VasilKalchev/PXLstick/img/3d-diag-bg.png

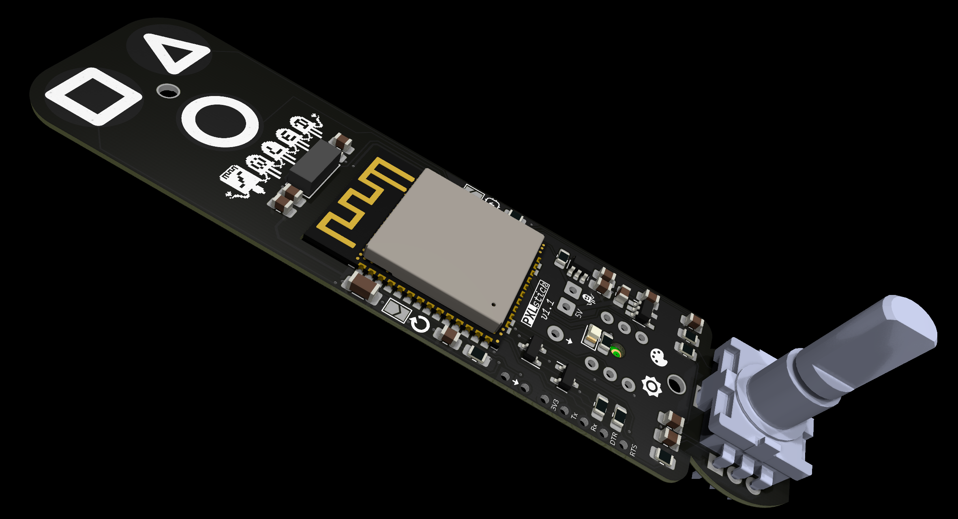
img/3d-diag-bg.png
