VasilKalchev/PXLstick/img/3d-diag.png

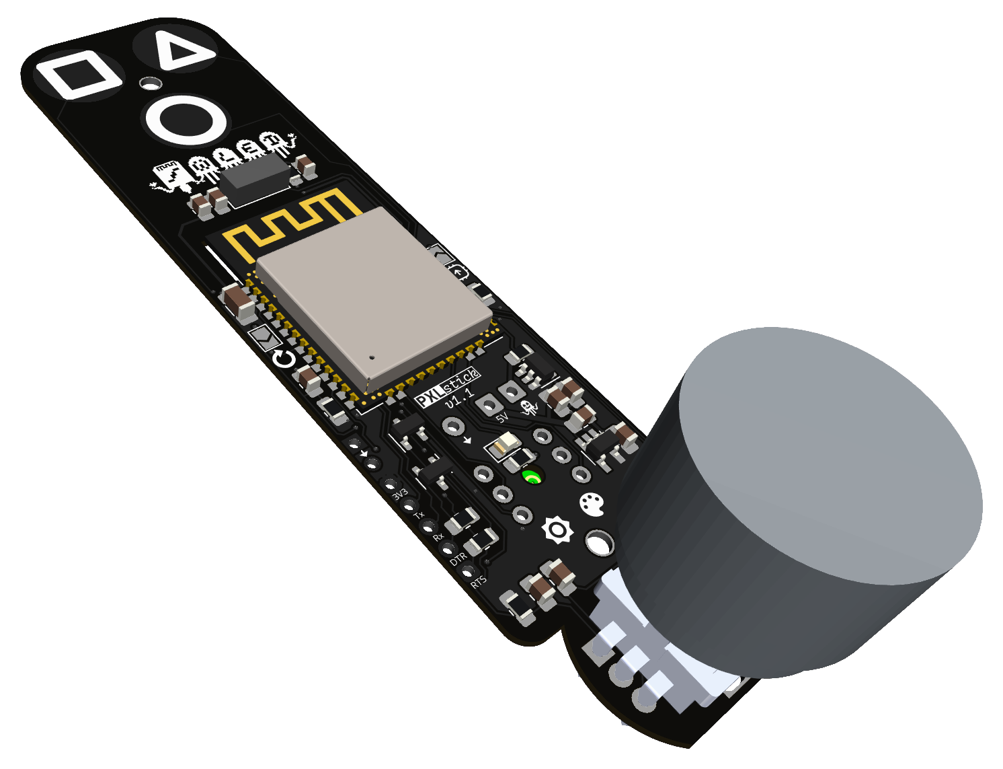
img/3d-diag.png
