VasilKalchev/PXLstick/img/3d-front.png

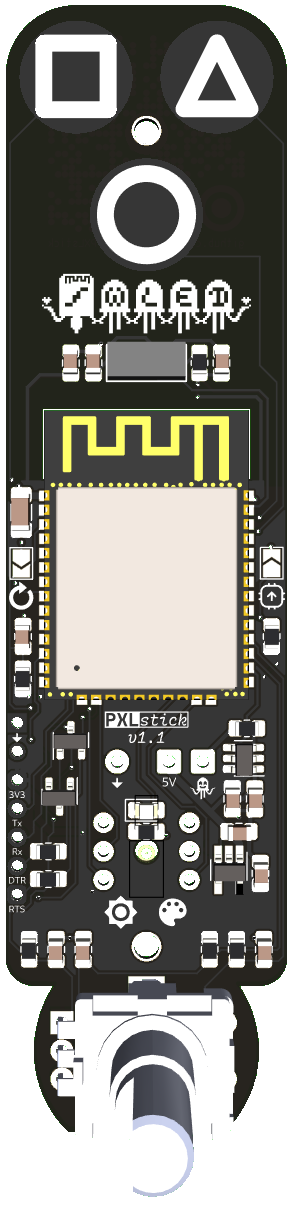
img/3d-front.png
