VasilKalchev/PXLstick/img/wall-pxlstick1-3d-side.png

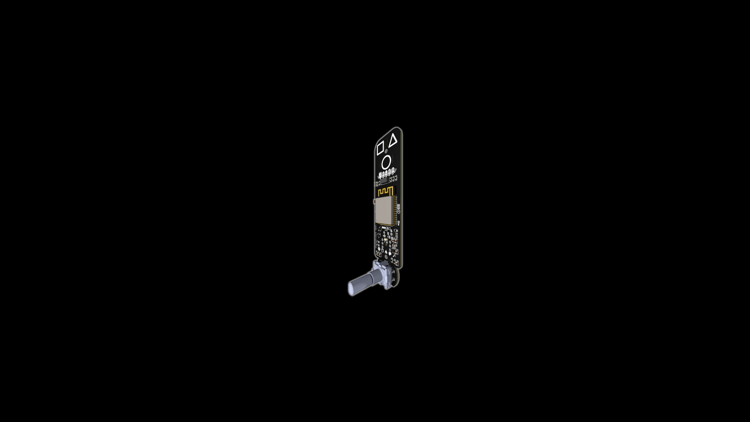
img/wall-pxlstick1-3d-side.png
