VasilKalchev/PXLstick/img/wall-pxlstick1.1-diag.png

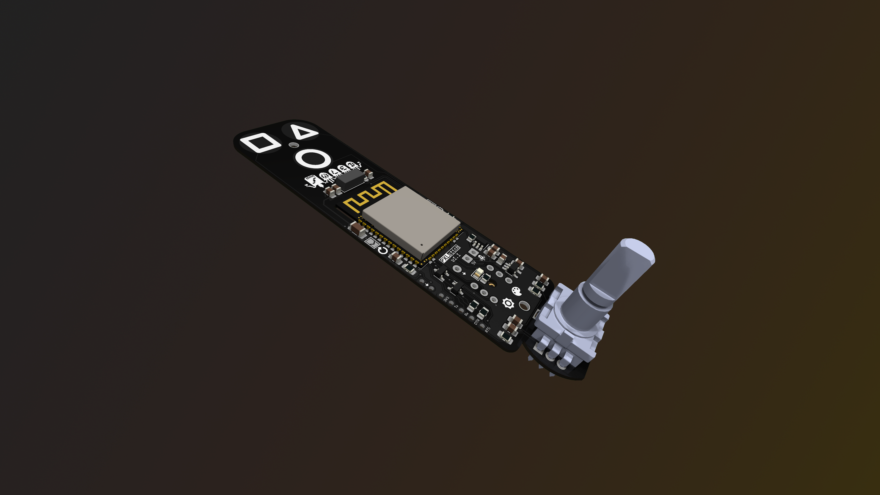
img/wall-pxlstick1.1-diag.png
